pateruu/Calorie_Tracker_PCB/simulations/ltspice/CalorieTracker_BTN0_LTSPICE.asc

C1: cap; 0.1�; V=16 Irms=0 Rser=0.038 Lser=800p mfg="W�rth Elektronik" pn="885012104001 WCAP-CSGP 0201" type="X5R"
R1: res; 10000; tol=1 pwr=63m
R2: res; 100; tol=1 pwr=63m
S1: sw; MYPB
V1: voltage; 3.3
V2: voltage; PULSE(0 1 2m 1u 1u 5m 10m)
Named nets: 0, BTN_0
.model MYPB SW(Ron=0.1 Roff=1Meg Vt=0.5 Vh=0.1)
.tran 20m
